ScatteredDrifter/Clacky40/pcb/dizzy40.kicad_sch

## KiCad design pcb/dizzy40.kicad_sch (2023-05-31)

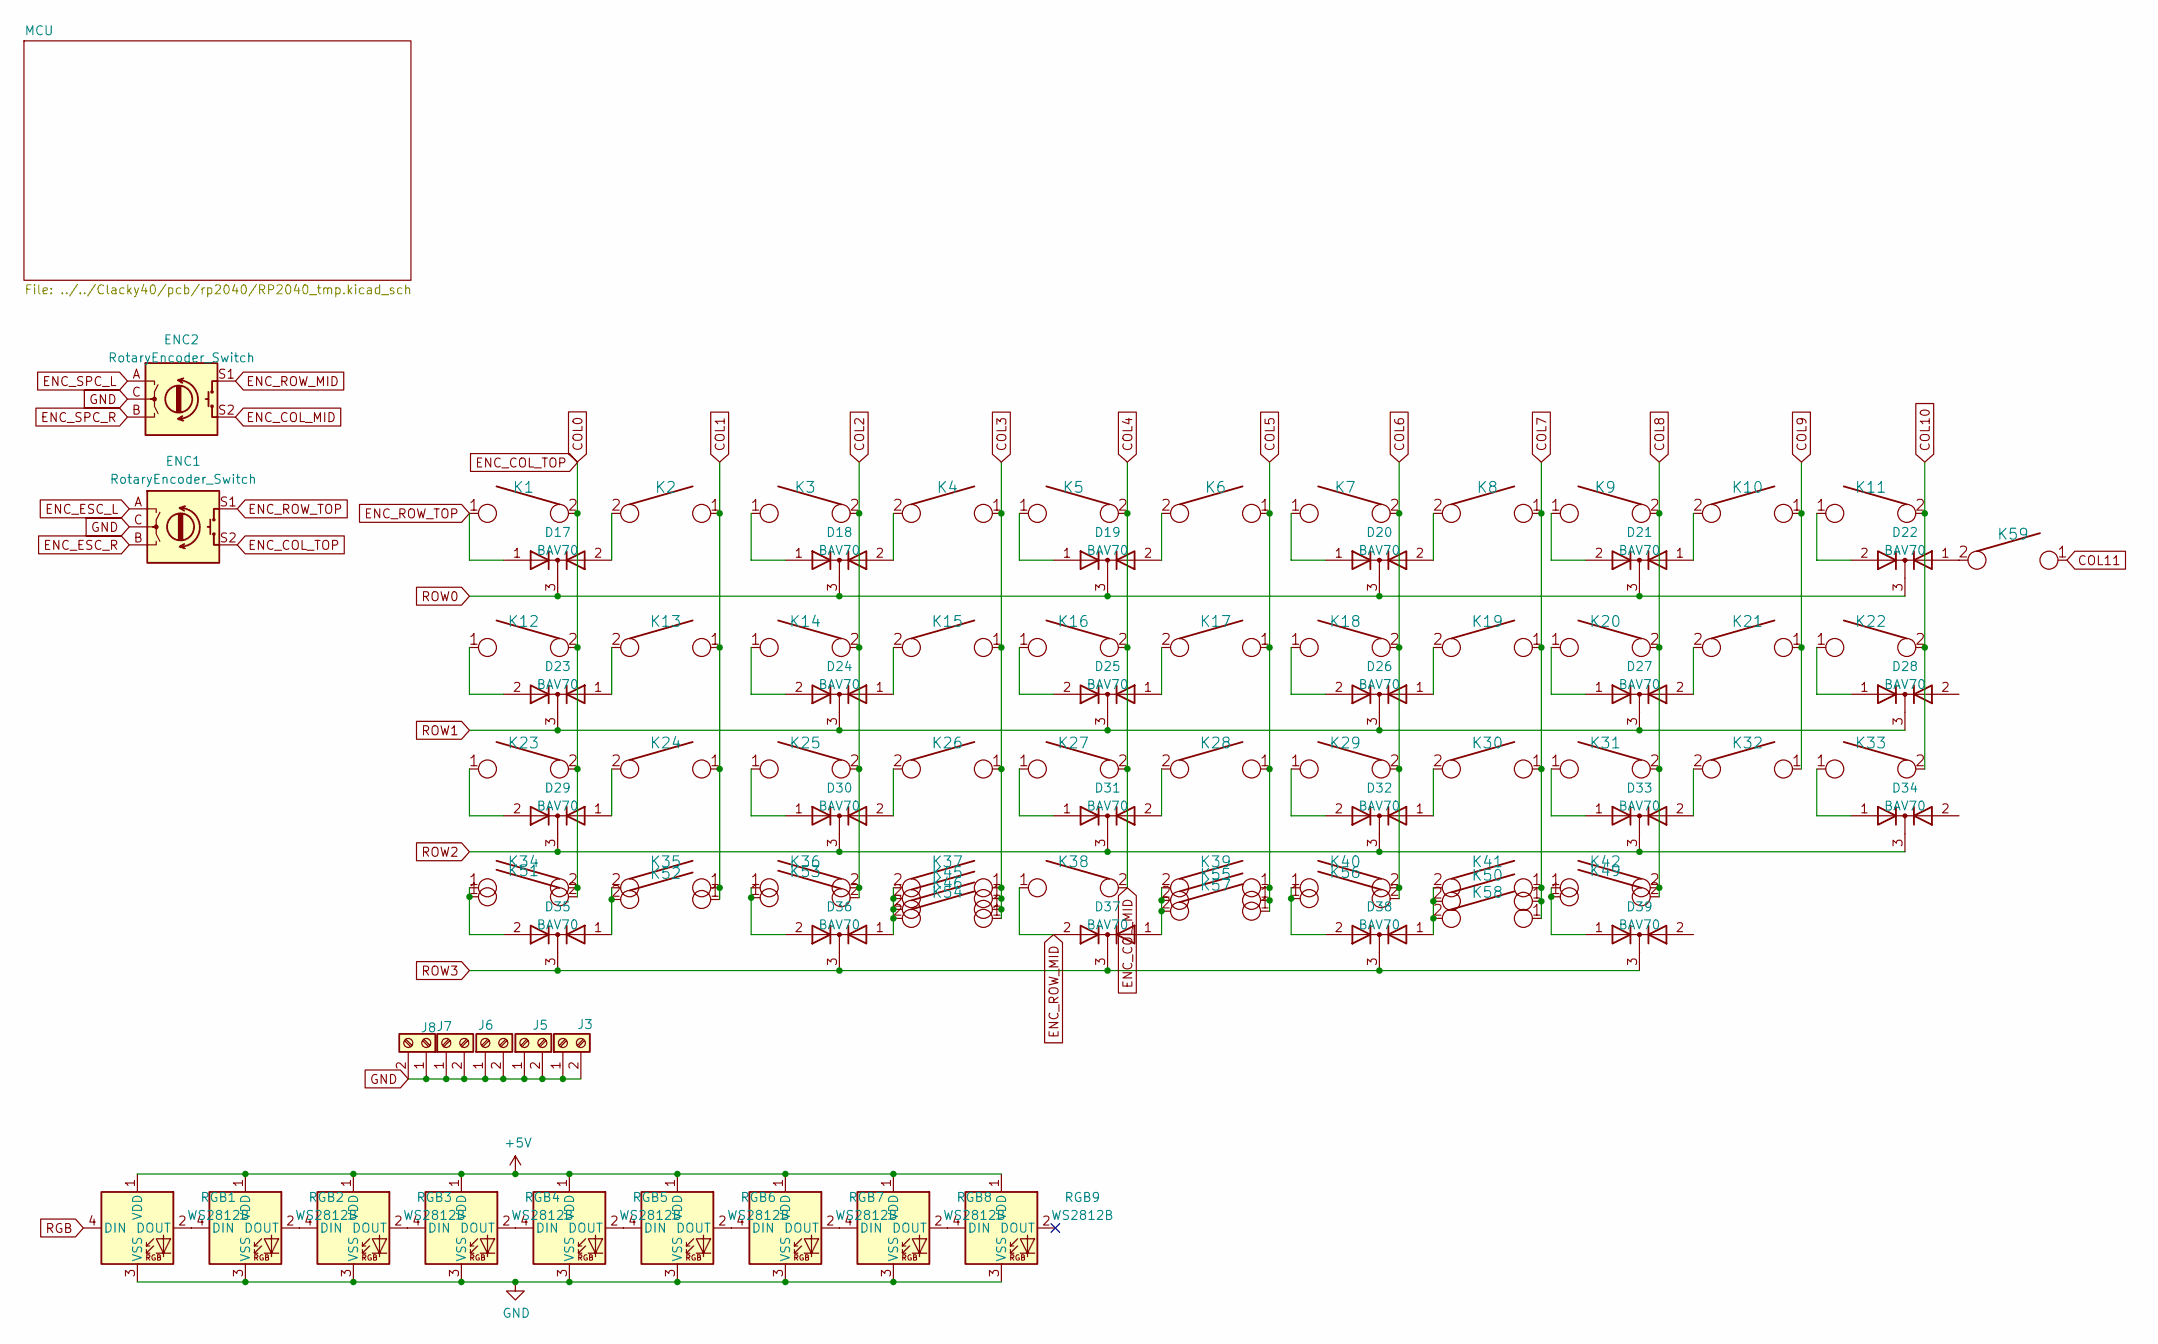
[picture p10: schematic dizzy40.kicad_sch]

Parts:
D17, D18, D19, D20, D21, D22, D23, D24, D25, D26, D27, D28, D29, D30, D31, D32, D33, D34, D35, D36, D37, D38, D39: BAV70; SOT-23
ENC1, ENC2: RotaryEncoder_Switch; RotaryEncoder_Alps_EC11E-Switch_Vertical_H20mm
J3, J5, J6, J7, J8: Screw_Terminal_01x02; STAB_MX_P_2u
K1, K2, K3, K4, K5, K6, K7, K8, K9, K10, K11, K12, K13, K14, K15, K16, K17, K18, K19, K20, K21, K22, K23, K24, K25, K26, K27, K28, K29, K30, K31, K32, K33, K34, K35, K36, K37, K38, K39, K40, K41, K42, K45, K46, K49, K50, K51, K52, K53, K54, K55, K56, K57, K58, K59: KEYSW; SW_MX_1u
RGB1, RGB2, RGB3, RGB4, RGB5, RGB6, RGB7, RGB8, RGB9: WS2812B; LED_WS2812B-PLCC4; LCSC C965555

Connections:
+5V: RGB1.1 (VDD), RGB2.1 (VDD), RGB3.1 (VDD), RGB4.1 (VDD), RGB5.1 (VDD), RGB6.1 (VDD), RGB7.1 (VDD), RGB8.1 (VDD), RGB9.1 (VDD)
COL0: ENC1.S2, K1.2, K12.2, K23.2, K34.2, K51.2
COL1: K2.1, K13.1, K24.1, K35.1, K52.1
COL2: K3.2, K14.2, K25.2, K36.2, K53.2
COL3: K4.1, K15.1, K26.1, K37.1, K45.1, K46.1, K54.1
COL4: ENC2.S2, K5.2, K16.2, K27.2, K38.2
COL5: K6.1, K17.1, K28.1, K39.1, K55.1, K57.1
COL6: K7.2, K18.2, K29.2, K40.2, K56.2
COL7: K8.1, K19.1, K30.1, K41.1, K50.1, K58.1
COL8: K9.2, K20.2, K31.2, K42.2, K49.2
COL9: K10.1, K21.1, K32.1
COL10: K11.2, K22.2, K33.2
COL11: K59.1
ENC_ESC_L: ENC1.A
ENC_ESC_R: ENC1.B
ENC_ROW_MID: D37.2 (A), ENC2.S1, K38.1
ENC_ROW_TOP: D17.1 (A), ENC1.S1, K1.1
ENC_SPC_L: ENC2.A
ENC_SPC_R: ENC2.B
GND: ENC1.C, ENC2.C, J3.1, J3.2, J5.1, J5.2, J6.1, J6.2, J7.1, J7.2, J8.1, J8.2, RGB1.3 (VSS), RGB2.3 (VSS), RGB3.3 (VSS), RGB4.3 (VSS), RGB5.3 (VSS), RGB6.3 (VSS), RGB7.3 (VSS), RGB8.3 (VSS), RGB9.3 (VSS)
unnamed: D17.2 (A), K2.2
unnamed: D18.1 (A), K3.1
unnamed: D18.2 (A), K4.2
unnamed: D19.1 (A), K5.1
unnamed: D19.2 (A), K6.2
unnamed: D20.1 (A), K7.1
unnamed: D20.2 (A), K8.2
unnamed: D21.1 (A), K10.2
unnamed: D21.2 (A), K9.1
unnamed: D22.1 (A), K59.2
unnamed: D22.2 (A), K11.1
unnamed: D23.1 (A), K13.2
unnamed: D23.2 (A), K12.1
unnamed: D24.1 (A), K15.2
unnamed: D24.2 (A), K14.1
unnamed: D25.1 (A), K17.2
unnamed: D25.2 (A), K16.1
unnamed: D26.1 (A), K19.2
unnamed: D26.2 (A), K18.1
unnamed: D27.1 (A), K20.1
unnamed: D27.2 (A), K21.2
unnamed: D28.1 (A), K22.1
unnamed: D29.1 (A), K24.2
unnamed: D29.2 (A), K23.1
unnamed: D30.1 (A), K25.1
unnamed: D30.2 (A), K26.2
unnamed: D31.1 (A), K27.1
unnamed: D31.2 (A), K28.2
unnamed: D32.1 (A), K30.2
unnamed: D32.2 (A), K29.1
unnamed: D33.1 (A), K31.1
unnamed: D33.2 (A), K32.2
unnamed: D34.1 (A), K33.1
unnamed: D35.1 (A), K35.2, K52.2
unnamed: D35.2 (A), K34.1, K51.1
unnamed: D36.1 (A), K37.2, K45.2, K46.2, K54.2
unnamed: D36.2 (A), K36.1, K53.1
unnamed: D37.1 (A), K39.2, K55.2, K57.2
unnamed: D38.1 (A), K41.2, K50.2, K58.2
unnamed: D38.2 (A), K40.1, K56.1
unnamed: D39.1 (A), K42.1, K49.1
unnamed: RGB1.2 (DOUT), RGB2.4 (DIN)
unnamed: RGB2.2 (DOUT), RGB3.4 (DIN)
unnamed: RGB3.2 (DOUT), RGB4.4 (DIN)
unnamed: RGB4.2 (DOUT), RGB5.4 (DIN)
unnamed: RGB5.2 (DOUT), RGB6.4 (DIN)
unnamed: RGB6.2 (DOUT), RGB7.4 (DIN)
unnamed: RGB7.2 (DOUT), RGB8.4 (DIN)
unnamed: RGB8.2 (DOUT), RGB9.4 (DIN)
RGB: RGB1.4 (DIN)
ROW0: D17.3 (K), D18.3 (K), D19.3 (K), D20.3 (K), D21.3 (K), D22.3 (K)
ROW1: D23.3 (K), D24.3 (K), D25.3 (K), D26.3 (K), D27.3 (K), D28.3 (K)
ROW2: D29.3 (K), D30.3 (K), D31.3 (K), D32.3 (K), D33.3 (K), D34.3 (K)
ROW3: D35.3 (K), D36.3 (K), D37.3 (K), D38.3 (K), D39.3 (K)
