ScatteredDrifter/Clacky40/pcb/rp2040/RP2040_tmp.kicad_sch

## KiCad design pcb/rp2040/RP2040_tmp.kicad_sch (2023-05-31)

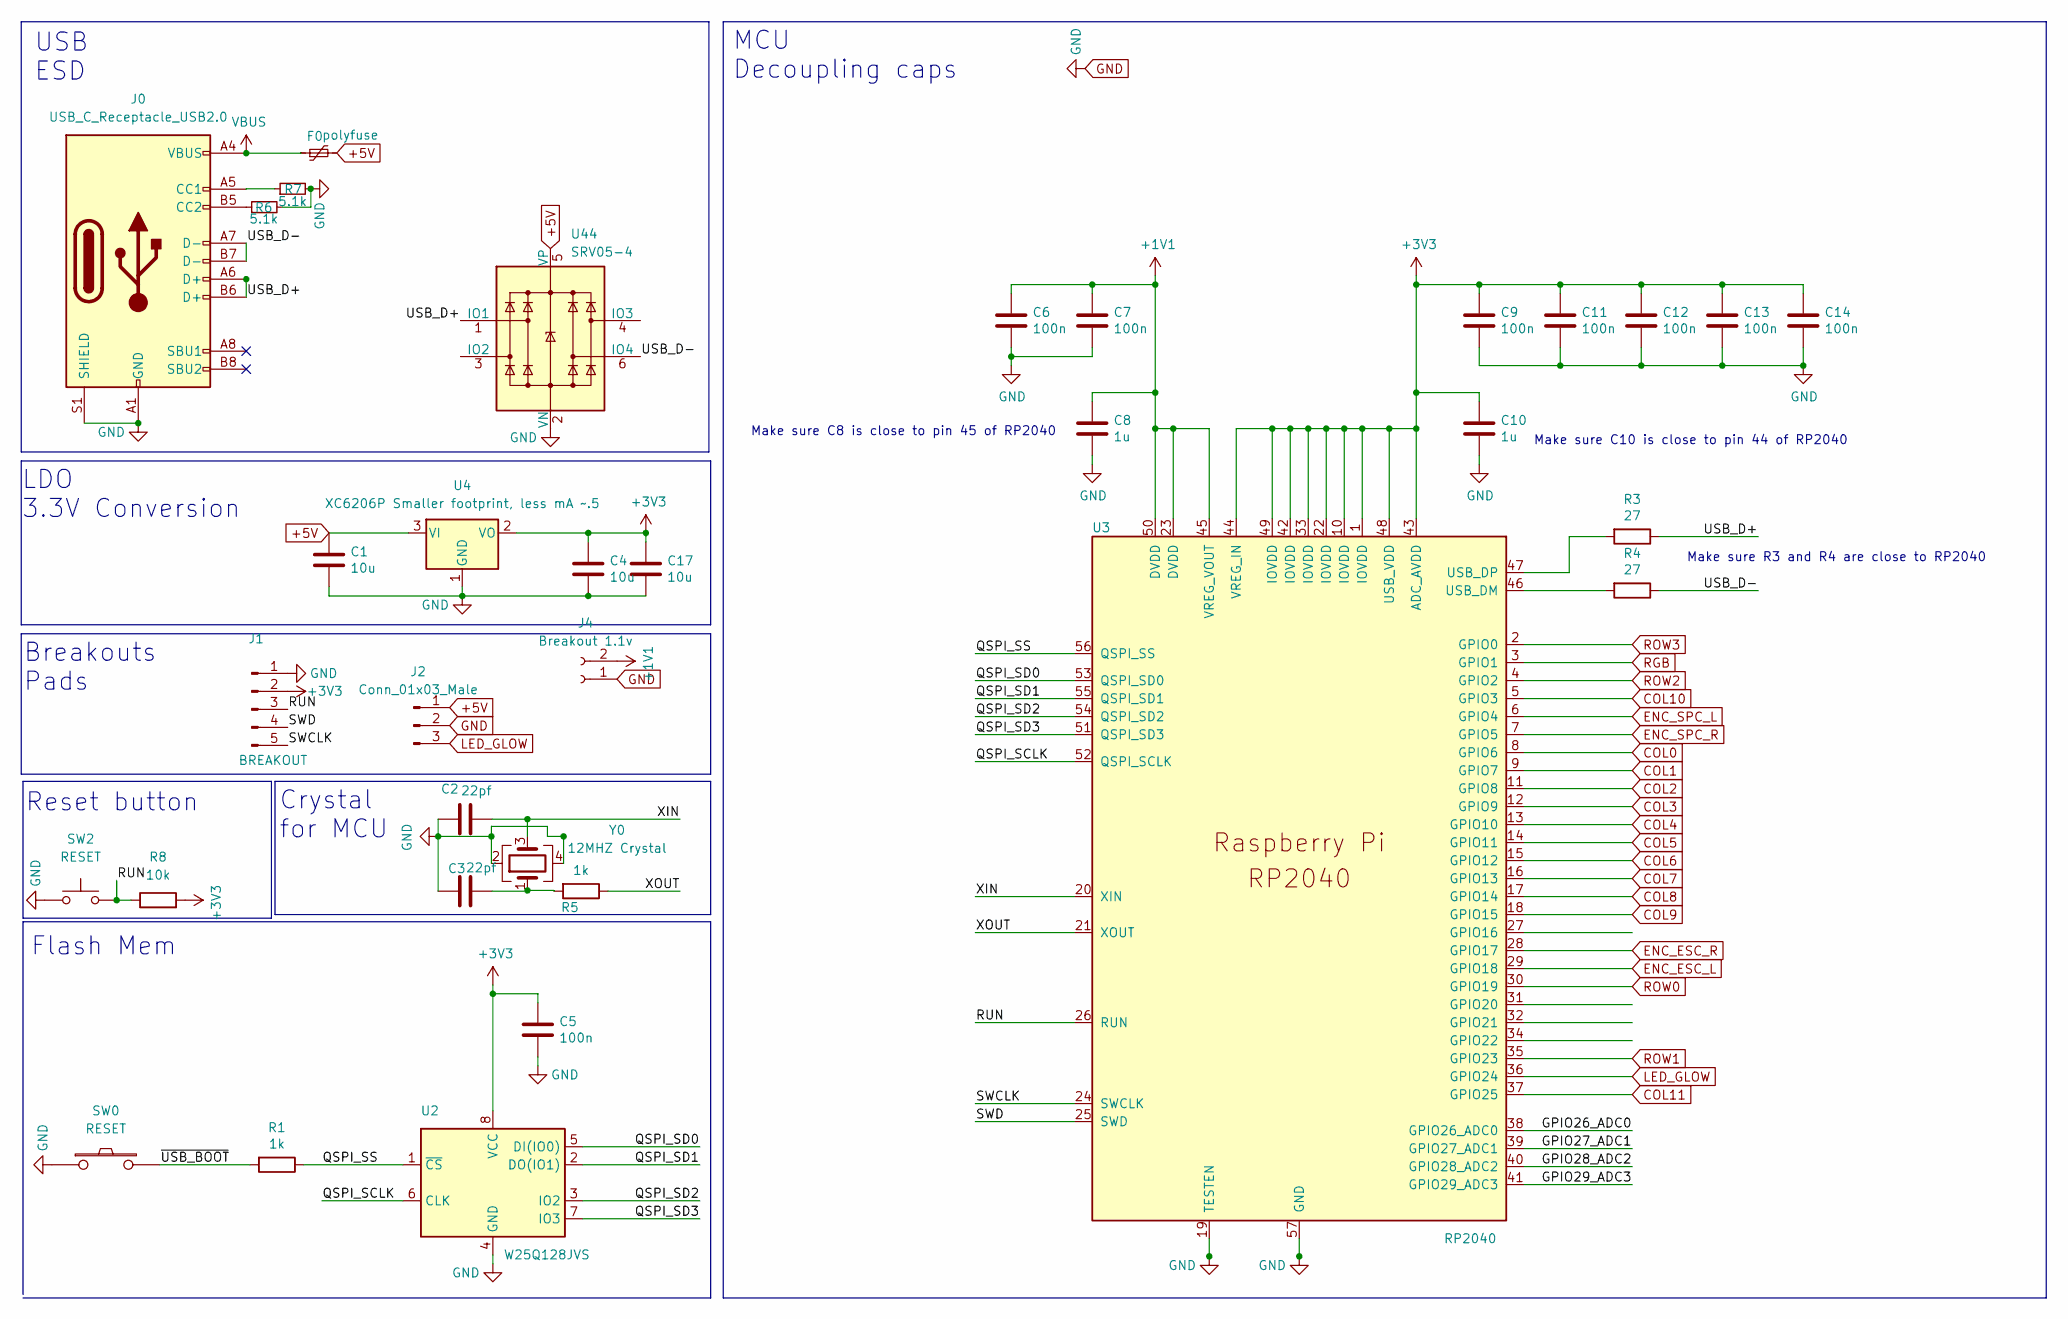
[picture p11: schematic RP2040_tmp.kicad_sch]

Parts:
C1, C4, C17: 10u; C_0805_2012Metric; LCSC C91245
C2, C3: 22pf; C_0805_2012Metric; LCSC C1804
C5, C6, C7, C9, C11, C12, C13, C14: 100n; C_0805_2012Metric; LCSC C49678
C8, C10: 1u; C_0805_2012Metric; LCSC C28323
F0: polyfuse; Fuse_1206_3216Metric; LCSC C69688
J0: USB_C_Receptacle_USB2.0; USB_C_Receptacle_HRO_TYPE-C-31-M-12; LCSC C165948
J1: BREAKOUT; PinSocket_1x05_P2.54mm_Vertical
J2: Conn_01x03_Male; PinSocket_1x03_P2.54mm_Vertical
J4: Breakout 1.1v; PinSocket_1x02_P2.54mm_Vertical
R1, R5: 1k; R_0805_2012Metric; LCSC C115316
R3, R4: 27; R_0805_2012Metric; LCSC C104170
R6, R7: 5.1k; R_0805_2012Metric; LCSC C27834
R8: 10k; R_0805_2012Metric; LCSC C115309
SW0, SW2: RESET; SW_SPST_TL3342; LCSC C2886894
U2: W25Q128JVS; SOIC-8_5.23x5.23mm_P1.27mm; LCSC C97521
U3: RP2040; RP2040-QFN-56; LCSC C2040
U4: XC6206P Smaller footprint, less mA ~.5; SOT-23; LCSC C347376
U44: SRV05-4; SOT-23-6; LCSC C85364
Y0: 12MHZ Crystal; Crystal_SMD_3225-4Pin_3.2x2.5mm; LCSC C9002

Connections:
+1V1: C6.1, C7.1, C8.1, J4.2, U3.23 (DVDD), U3.45 (VREG_VOUT), U3.50 (DVDD)
+3V3: C4.1, C5.1, C9.1, C10.1, C11.1, C12.1, C13.1, C14.1, C17.1, J1.2, R8.2, U2.8 (VCC), U3.1 (IOVDD), U3.10 (IOVDD), U3.22 (IOVDD), U3.33 (IOVDD), U3.42 (IOVDD), U3.43 (ADC_AVDD), U3.44 (VREG_IN), U3.48 (USB_VDD), U3.49 (IOVDD), U4.2 (VO)
+5V: C1.1, F0.2, J2.1, U4.3 (VI), U44.5 (VP)
COL0: U3.8 (GPIO6)
COL1: U3.9 (GPIO7)
COL2: U3.11 (GPIO8)
COL3: U3.12 (GPIO9)
COL4: U3.13 (GPIO10)
COL5: U3.14 (GPIO11)
COL6: U3.15 (GPIO12)
COL7: U3.16 (GPIO13)
COL8: U3.17 (GPIO14)
COL9: U3.18 (GPIO15)
COL10: U3.5 (GPIO3)
COL11: U3.37 (GPIO25)
ENC_ESC_L: U3.29 (GPIO18)
ENC_ESC_R: U3.28 (GPIO17)
ENC_SPC_L: U3.6 (GPIO4)
ENC_SPC_R: U3.7 (GPIO5)
GND: C1.2, C2.2, C3.2, C4.2, C5.2, C6.2, C7.2, C8.2, C9.2, C10.2, C11.2, C12.2, C13.2, C14.2, C17.2, J0.A1 (GND), J0.A12 (GND), J0.B1 (GND), J0.B12 (GND), J0.S1 (SHIELD), J1.1, J2.2, J4.1, R6.2, R7.2, SW0.1, SW2.1, U2.4 (GND), U3.19 (TESTEN), U3.57 (GND), U4.1 (GND), U44.2 (VN), Y0.2, Y0.4
GPIO26_ADC0: U3.38 (GPIO26_ADC0)
GPIO27_ADC1: U3.39 (GPIO27_ADC1)
GPIO28_ADC2: U3.40 (GPIO28_ADC2)
GPIO29_ADC3: U3.41 (GPIO29_ADC3)
LED_GLOW: J2.3, U3.36 (GPIO24)
unnamed: C3.1, R5.2, Y0.1
unnamed: J0.A5 (CC1), R7.1
unnamed: J0.B5 (CC2), R6.1
unnamed: R3.2, U3.47 (USB_DP)
unnamed: R4.2, U3.46 (USB_DM)
QSPI_SCLK: U2.6 (CLK), U3.52 (QSPI_SCLK)
QSPI_SD0: U2.5 (DI(IO0)), U3.53 (QSPI_SD0)
QSPI_SD1: U2.2 (DO(IO1)), U3.55 (QSPI_SD1)
QSPI_SD2: U2.3 (IO2), U3.54 (QSPI_SD2)
QSPI_SD3: U2.7 (IO3), U3.51 (QSPI_SD3)
QSPI_SS: R1.1, U2.1 (~CS), U3.56 (QSPI_SS)
RGB: U3.3 (GPIO1)
ROW0: U3.30 (GPIO19)
ROW1: U3.35 (GPIO23)
ROW2: U3.4 (GPIO2)
ROW3: U3.2 (GPIO0)
RUN: J1.3, R8.1, SW2.2, U3.26 (RUN)
SWCLK: J1.5, U3.24 (SWCLK)
SWD: J1.4, U3.25 (SWD)
USB_D+: J0.A6 (D+), J0.B6 (D+), R3.1, U44.1 (IO1)
USB_D-: J0.A7 (D-), J0.B7 (D-), R4.1, U44.6 (IO4)
VBUS: F0.1, J0.A4 (VBUS), J0.A9 (VBUS), J0.B4 (VBUS), J0.B9 (VBUS)
XIN: C2.1, U3.20 (XIN), Y0.3
XOUT: R5.1, U3.21 (XOUT)
~USB_BOOT: R1.2, SW0.2

Notes on the sheet:
USB ESD
Make sure C8 is close to pin 45 of RP2040
Breakouts Pads
Make sure R3 and R4 are close to RP2040
Crystal for MCU
Flash Mem
MCU Decoupling caps
Make sure C10 is close to pin 44 of RP2040
Reset button
LDO 3.3V Conversion
